0x2b3bfa0/2080-controller/resources/Pictures/IMG_20160507_113246.jpg

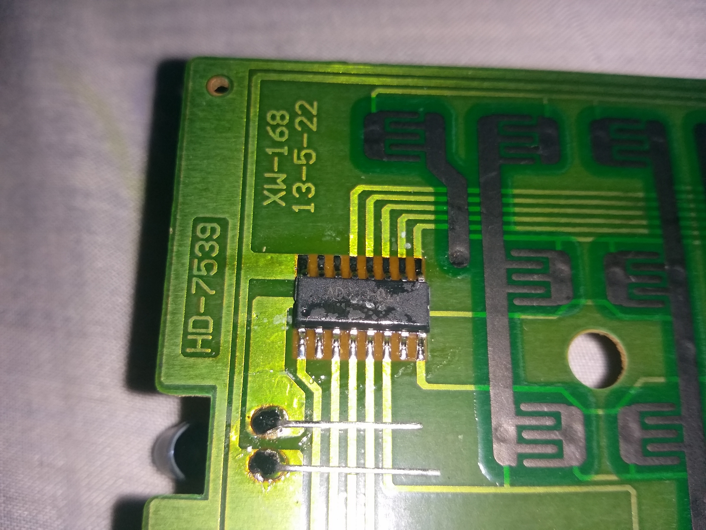
resources/Pictures/IMG_20160507_113246.jpg
