0x2b3bfa0/2080-controller/resources/Pictures/IMG_20160510_004947.jpg

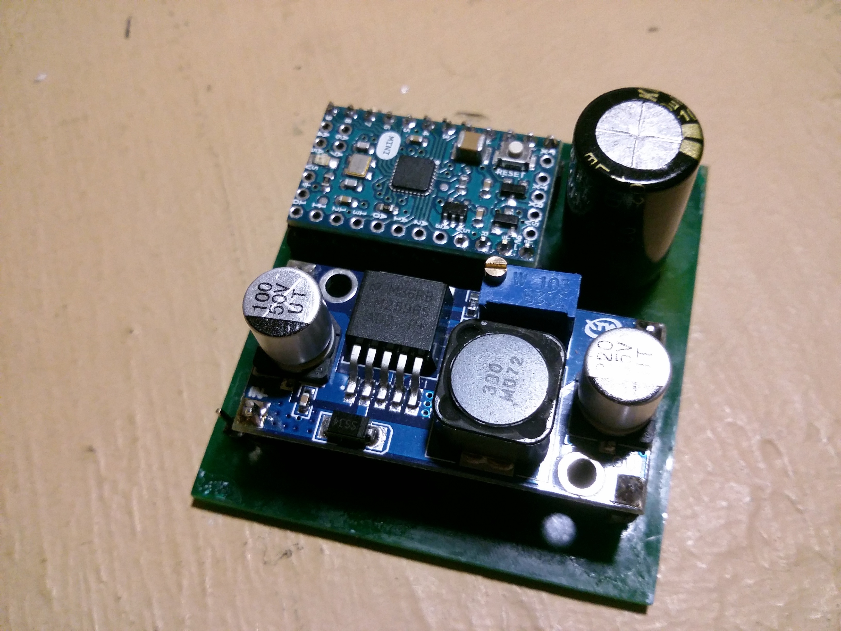
resources/Pictures/IMG_20160510_004947.jpg
