0x2b3bfa0/2080-controller/resources/Pictures/IMG_20160510_004954.jpg

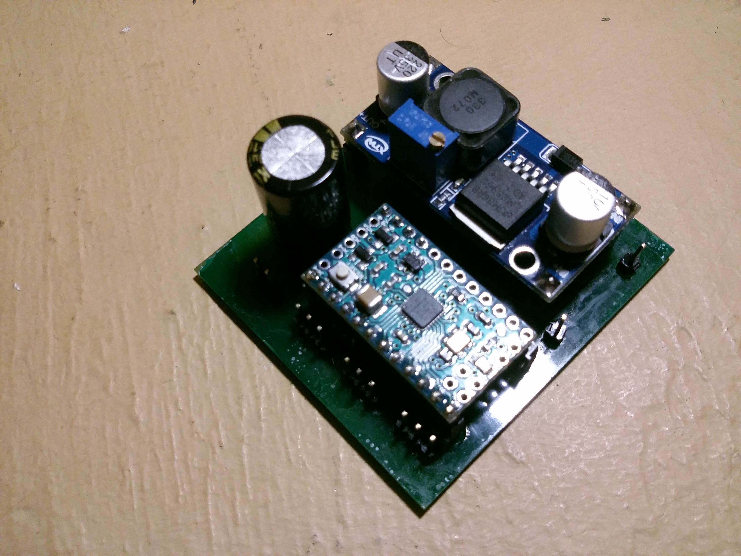
resources/Pictures/IMG_20160510_004954.jpg
